alexivan04/inktime/Images/img1.png

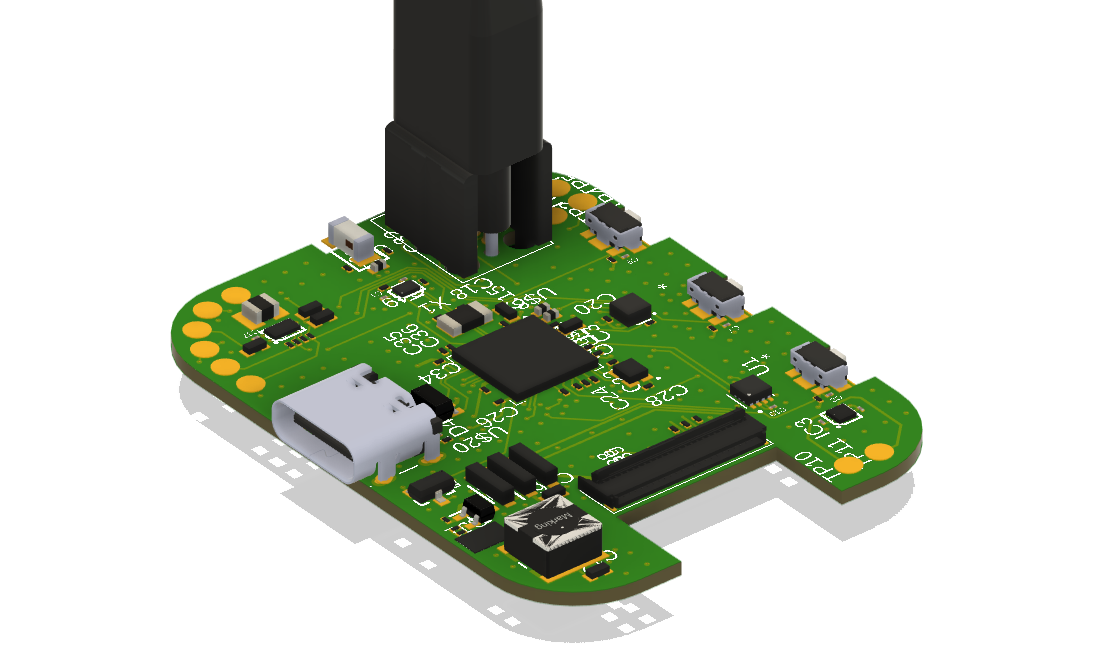
Images/img1.png
