alexivan04/inktime/Images/img2.png

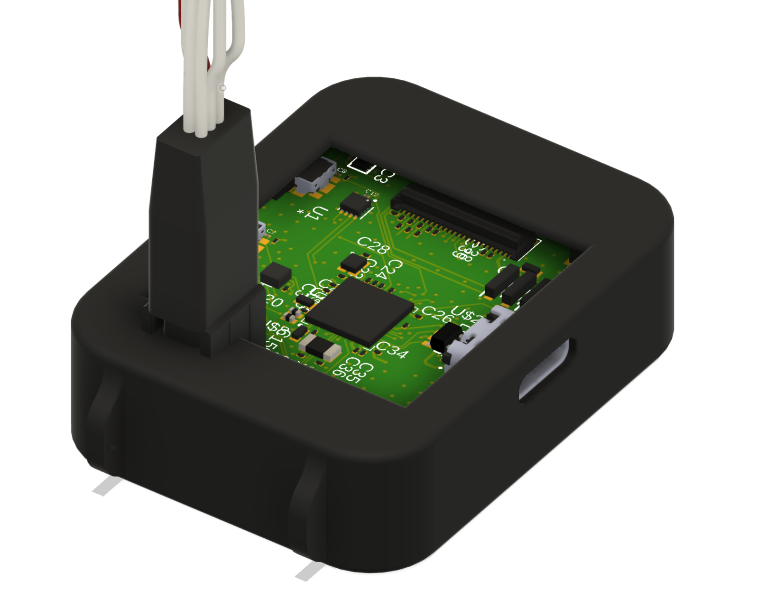
Images/img2.png
