alexivan04/inktime/Images/img3.png

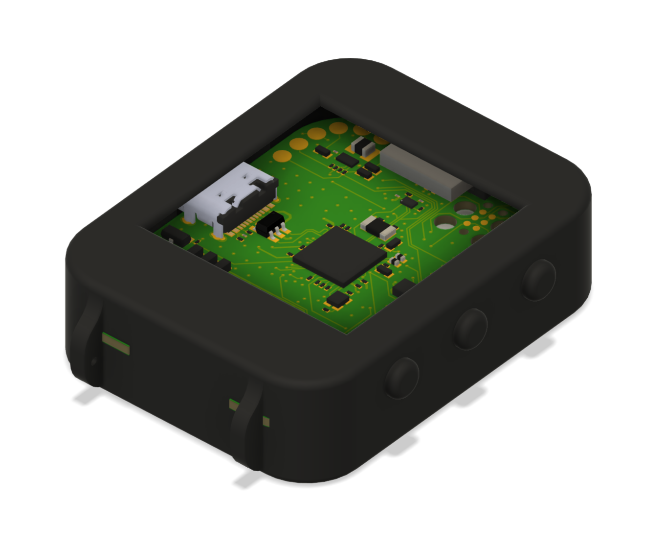
Images/img3.png
